tebl/ZX-Interface-2.021/gallery/2021-04-01 02.16.09.jpg

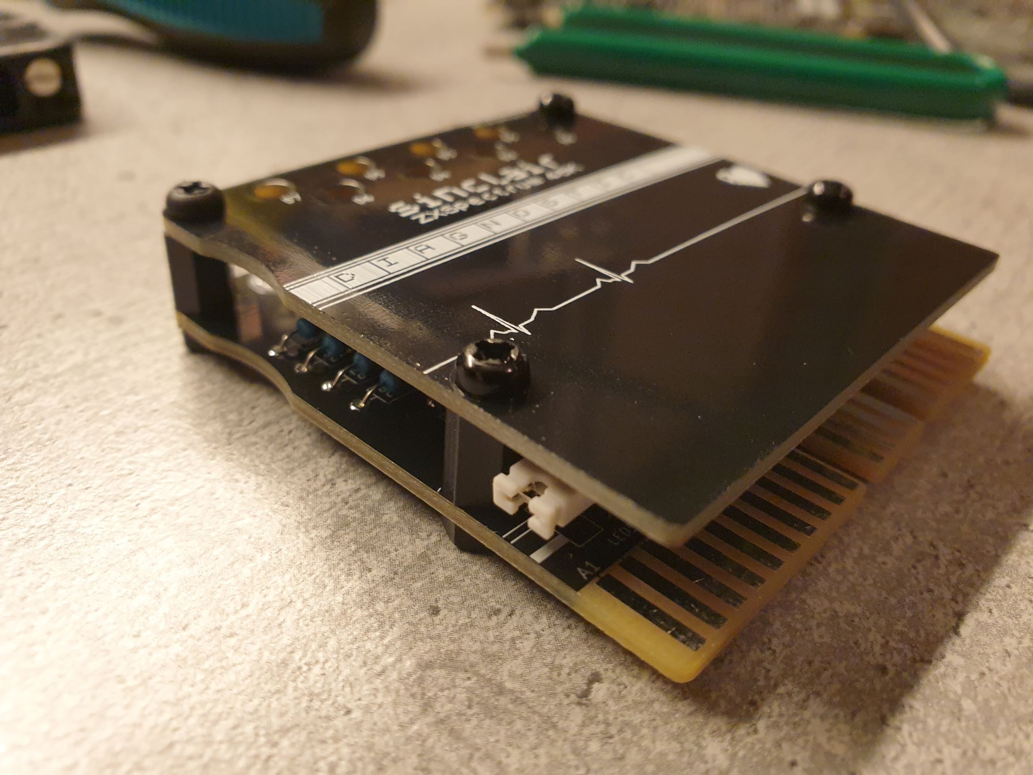
gallery/2021-04-01 02.16.09.jpg
