tebl/ZX-Interface-2.021/gallery/2021-04-01 15.58.48.jpg

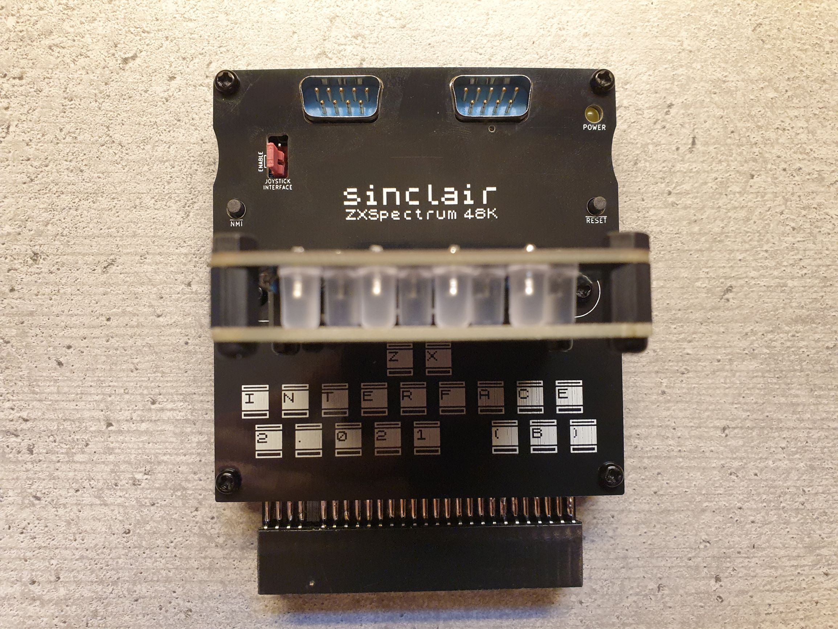
gallery/2021-04-01 15.58.48.jpg
