tebl/ZX-Interface-2.021/gallery/2021-04-01 22.12.05.jpg

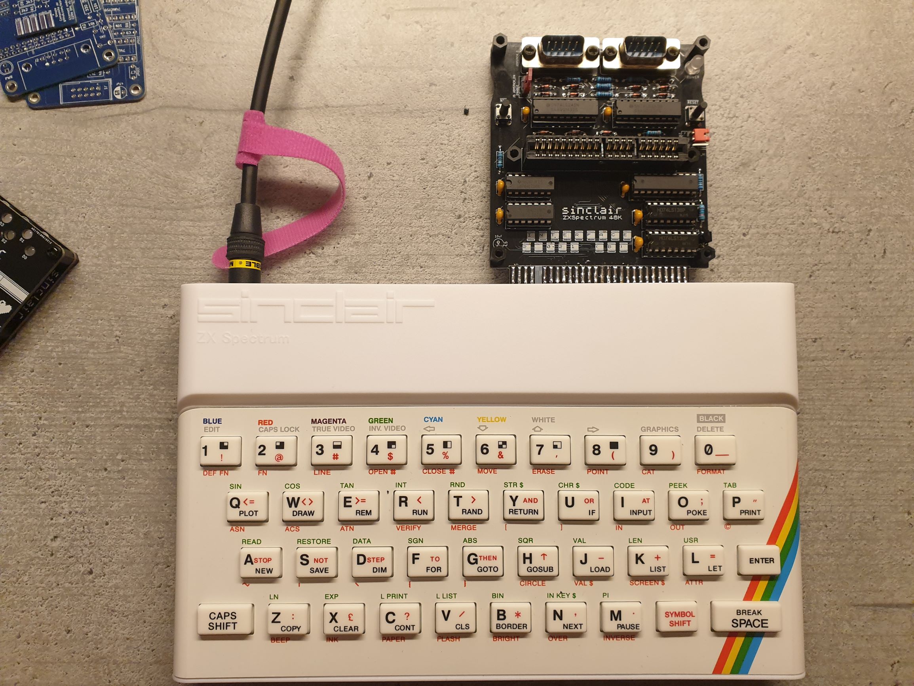
gallery/2021-04-01 22.12.05.jpg
