tebl/ZX-Interface-2.021/gallery/2021-04-01 22.18.30.jpg

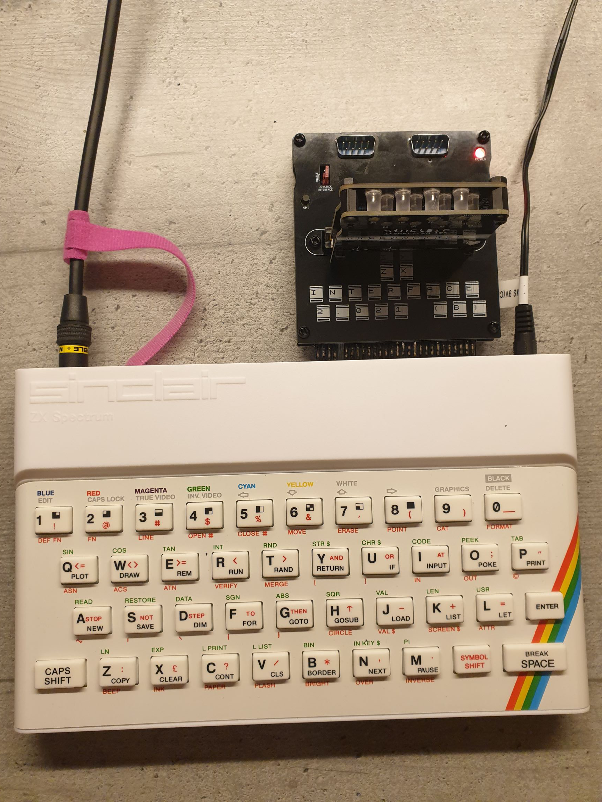
gallery/2021-04-01 22.18.30.jpg
