tebl/ZX-Interface-2.021/gallery/2021-04-14 02.23.00.jpg

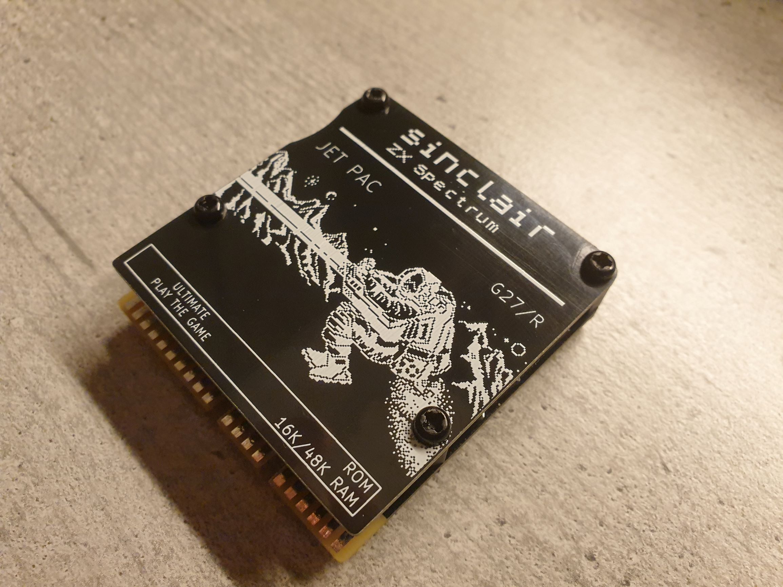
gallery/2021-04-14 02.23.00.jpg
