tebl/ZX-Interface-2.021/gallery/2021-04-23 00.03.16.jpg

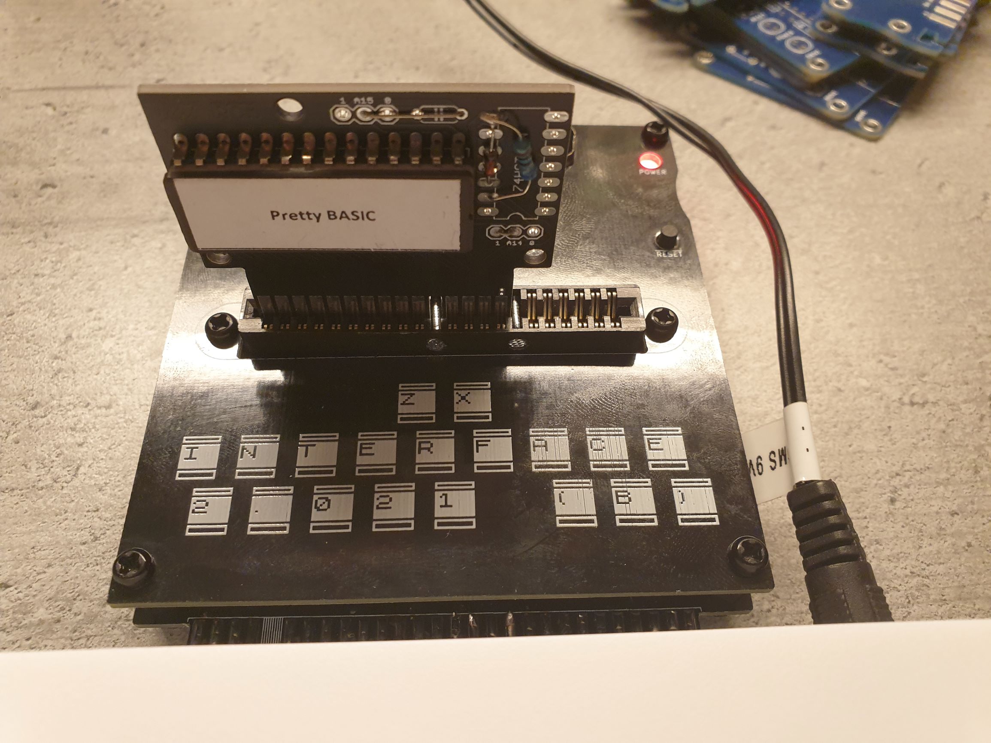
gallery/2021-04-23 00.03.16.jpg
