tebl/ZX-Interface-2.021/gallery/2021-04-29 00.07.34.jpg

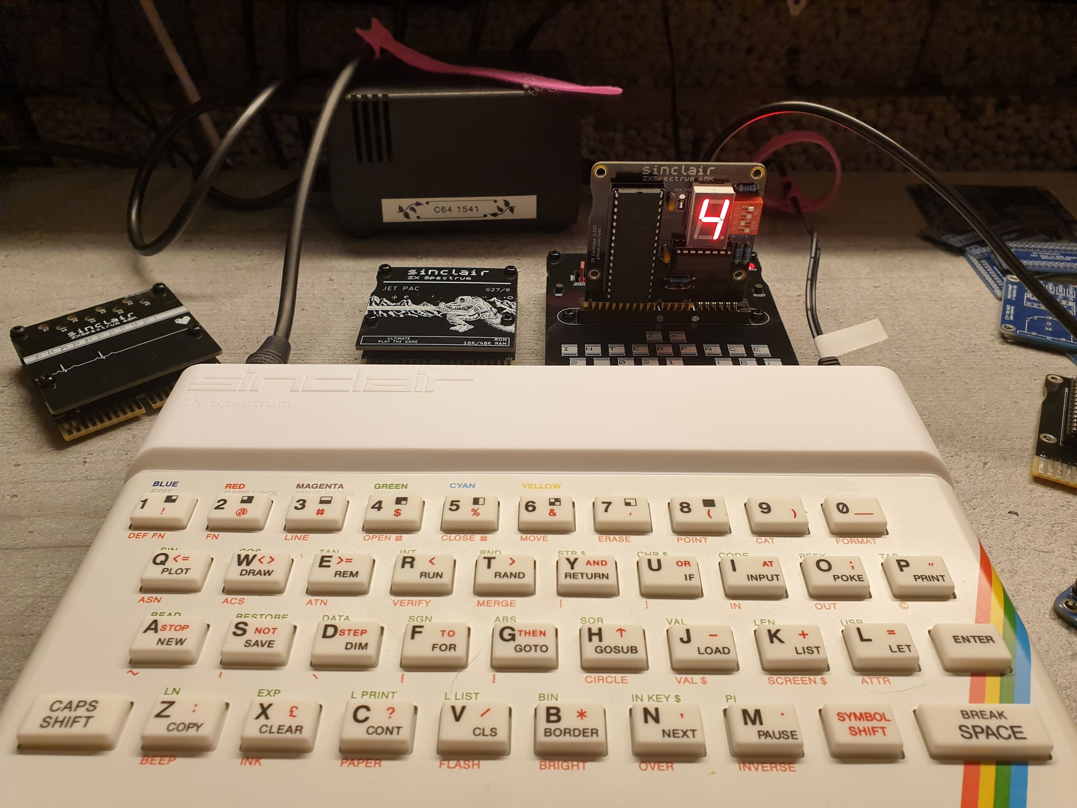
gallery/2021-04-29 00.07.34.jpg
