tebl/ZX-Interface-2.021/gallery/2021-05-09 21.05.03.jpg

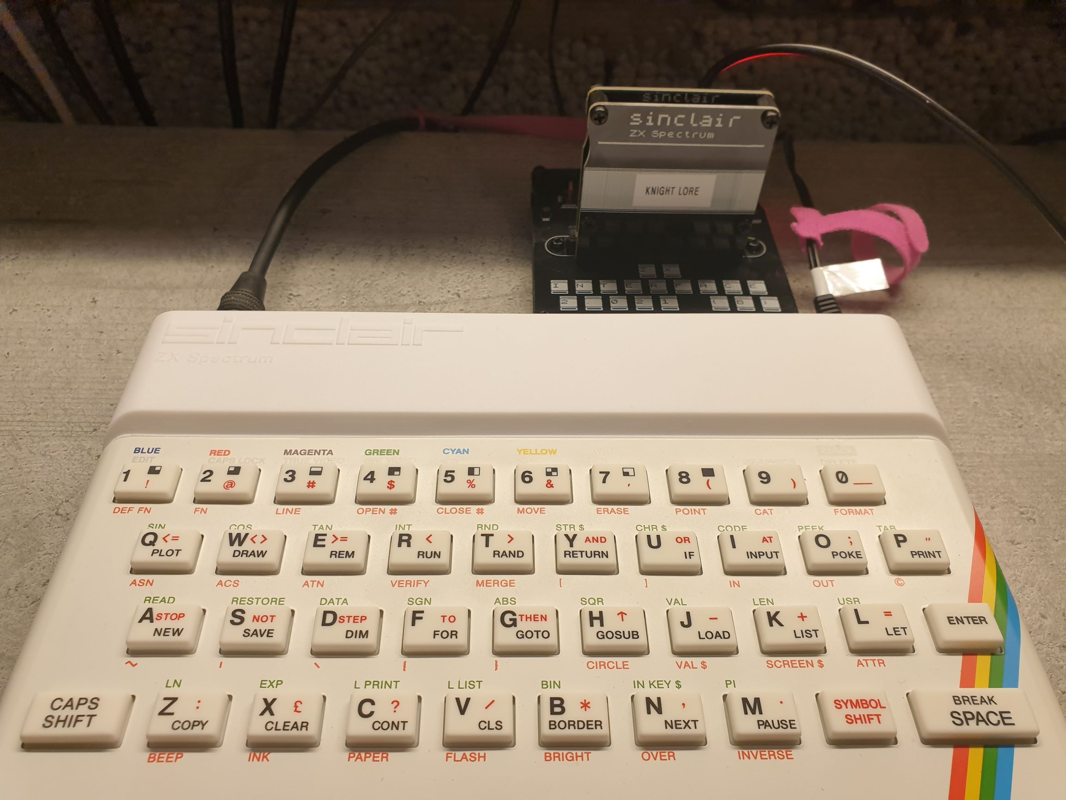
gallery/2021-05-09 21.05.03.jpg
