tebl/ZX-Interface-2.021/gallery/2021-09-04 23.34.56.jpg

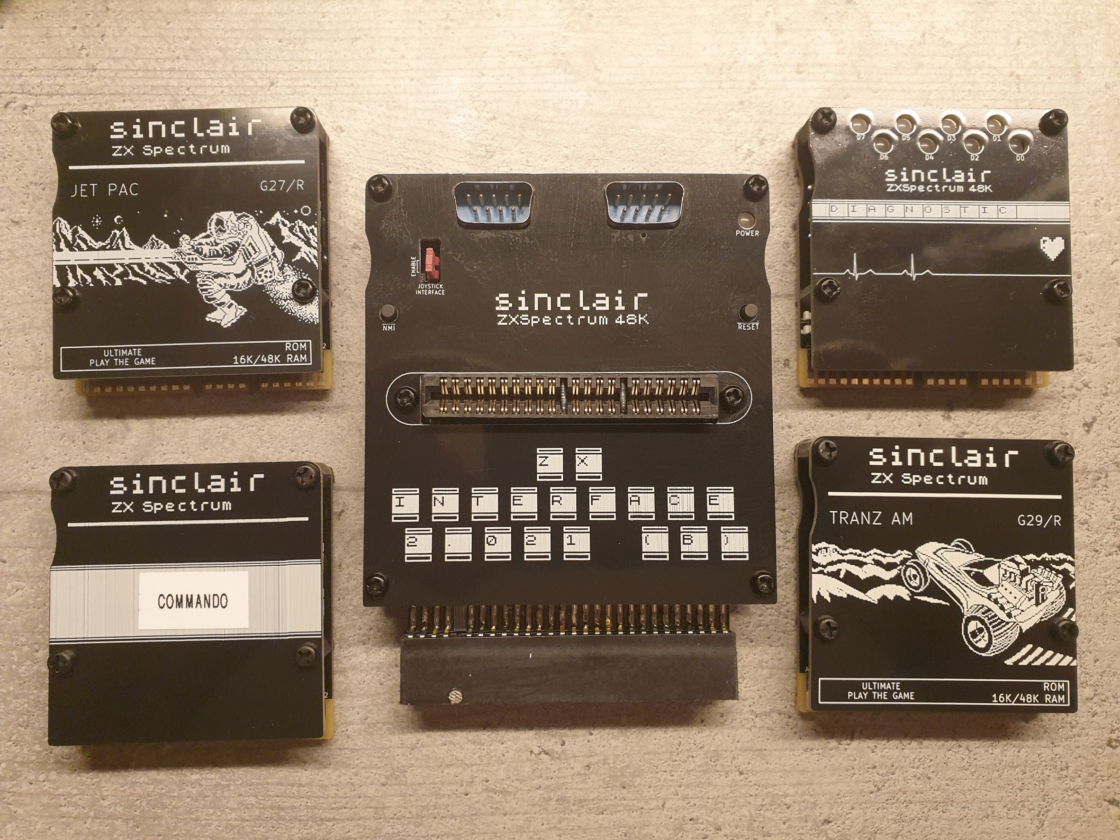
gallery/2021-09-04 23.34.56.jpg
