tebl/ZX-Interface-2.021/gallery/2021-09-04 23.39.01.jpg

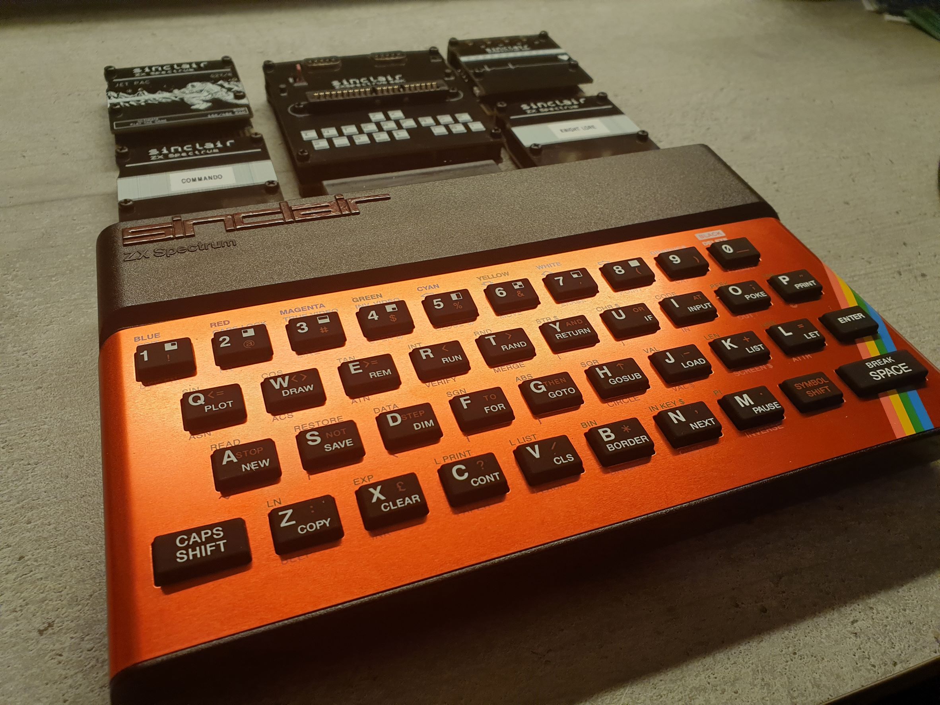
gallery/2021-09-04 23.39.01.jpg
