tebl/ZX-Interface-2.021/gallery/2021-09-06 23.09.44.jpg

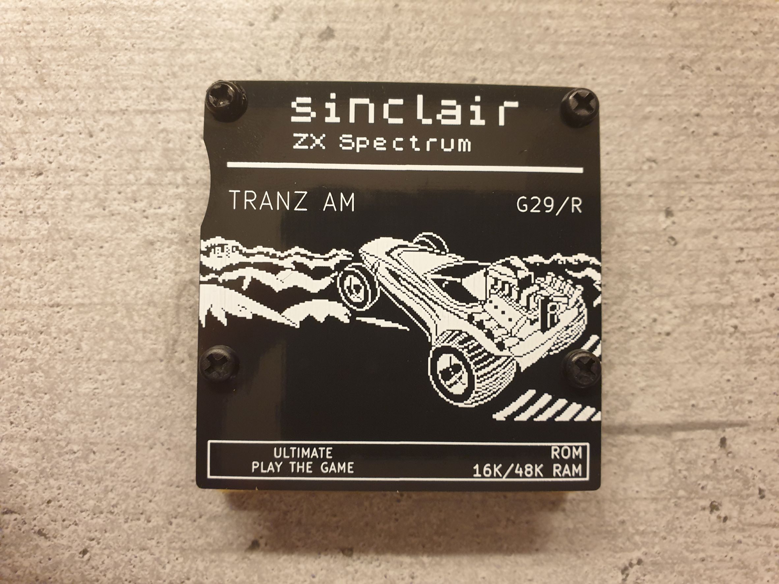
gallery/2021-09-06 23.09.44.jpg
