tebl/ZX-Interface-2.021/gallery/ZX Cartridge 2021 FA1.png

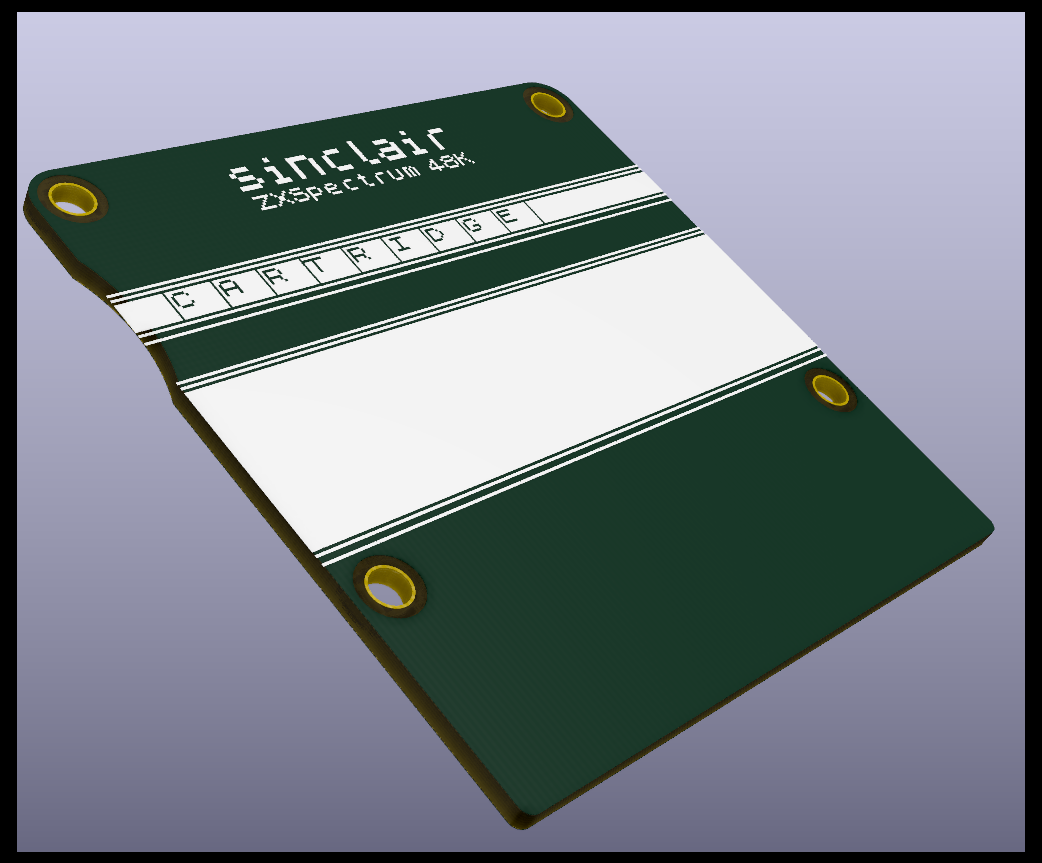
gallery/ZX Cartridge 2021 FA1.png
