tebl/ZX-Interface-2.021/gallery/ZX Cartridge 2021 FA1_001.jpg

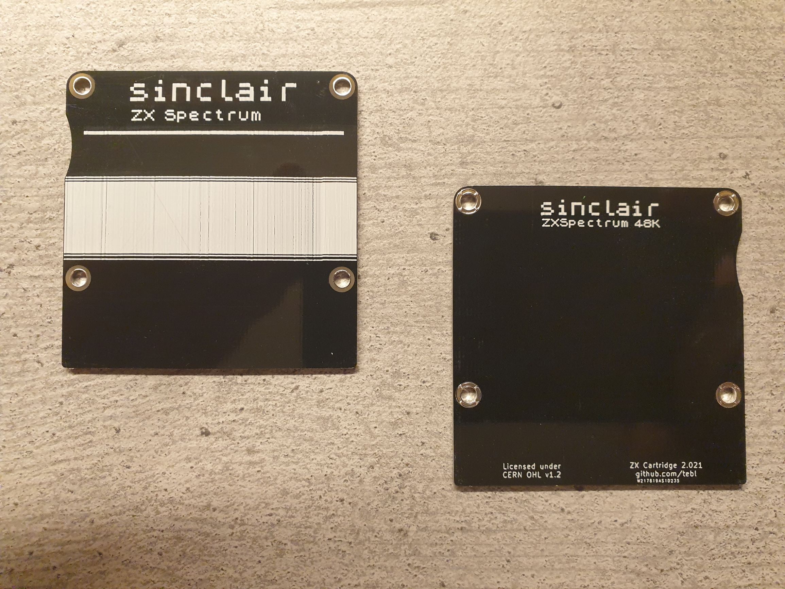
gallery/ZX Cartridge 2021 FA1_001.jpg
