tebl/ZX-Interface-2.021/gallery/ZX Cartridge 2021 FA1_003.jpg

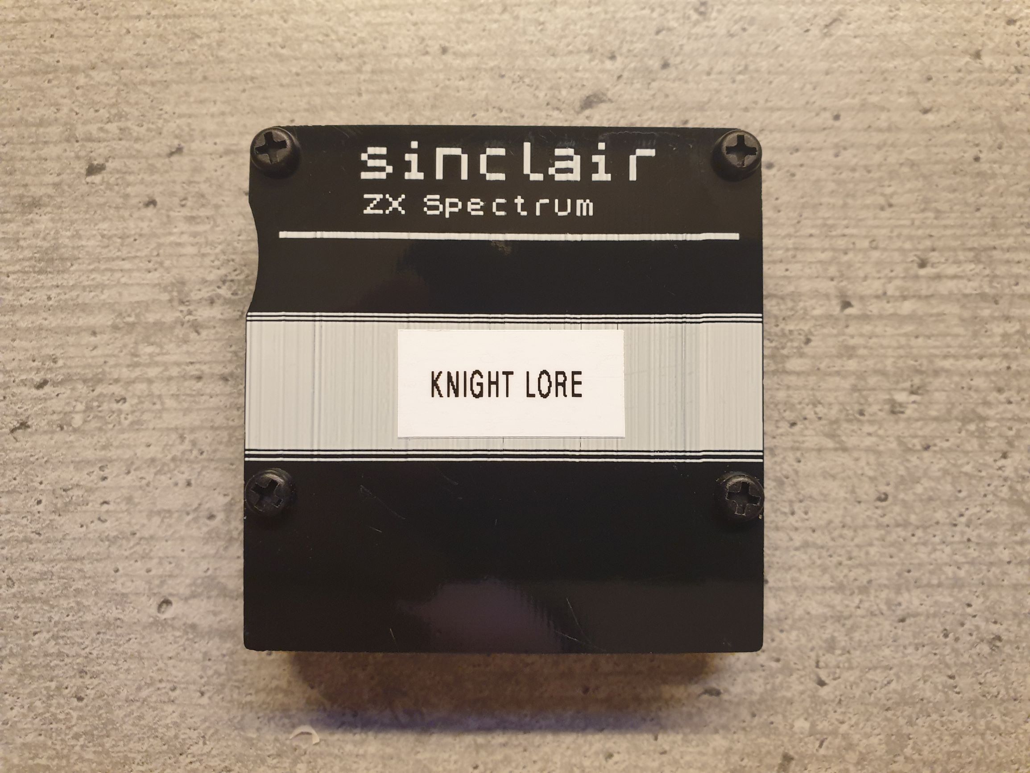
gallery/ZX Cartridge 2021 FA1_003.jpg
