tebl/ZX-Interface-2.021/gallery/ZX Cartridge 2021 FA5 Cassette.png

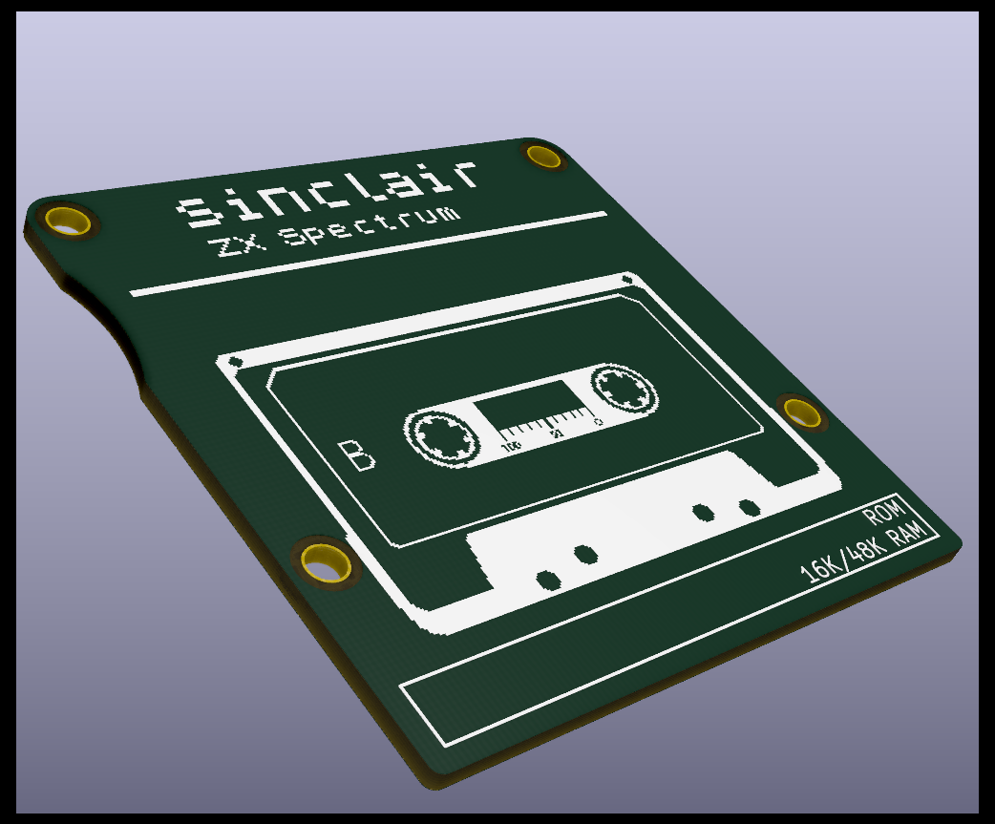
gallery/ZX Cartridge 2021 FA5 Cassette.png
