tebl/ZX-Interface-2.021/gallery/ZX Diagnostic 2021 FA1_001.jpg

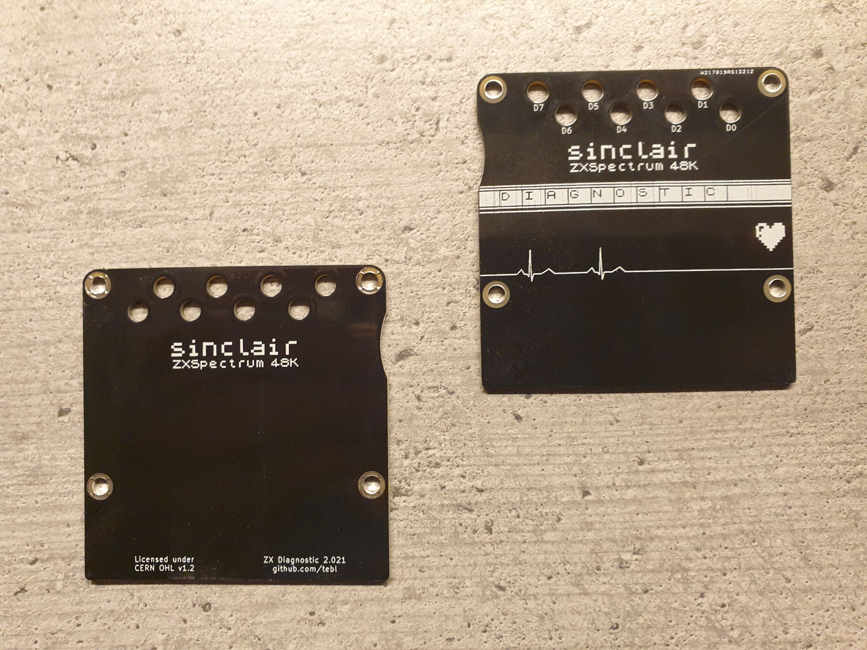
gallery/ZX Diagnostic 2021 FA1_001.jpg
