tebl/ZX-Interface-2.021/gallery/ZX Interface 2021 FA1.jpg

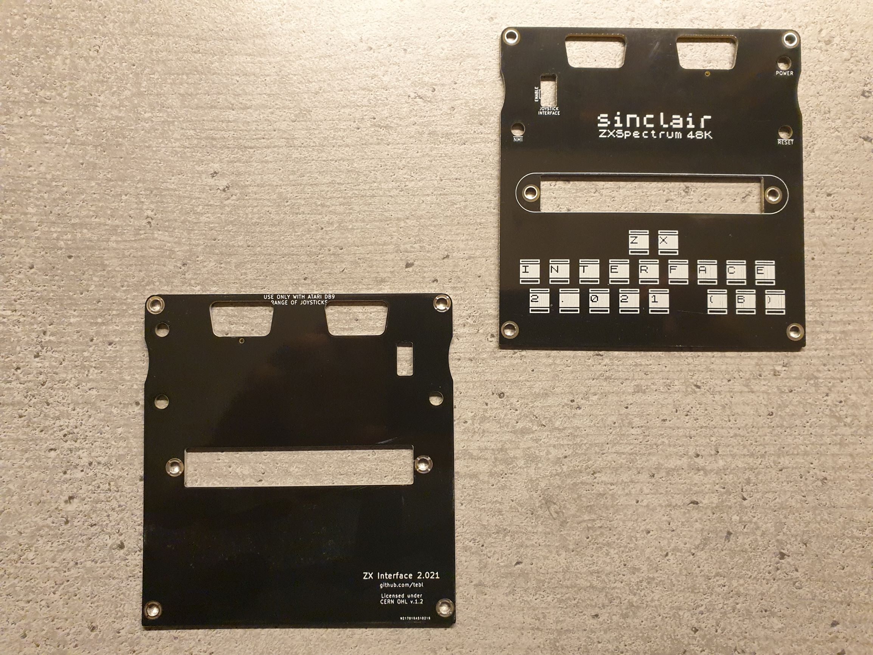
gallery/ZX Interface 2021 FA1.jpg
