tebl/ZX-Interface-2.021/gallery/ZX Interface 2021.png

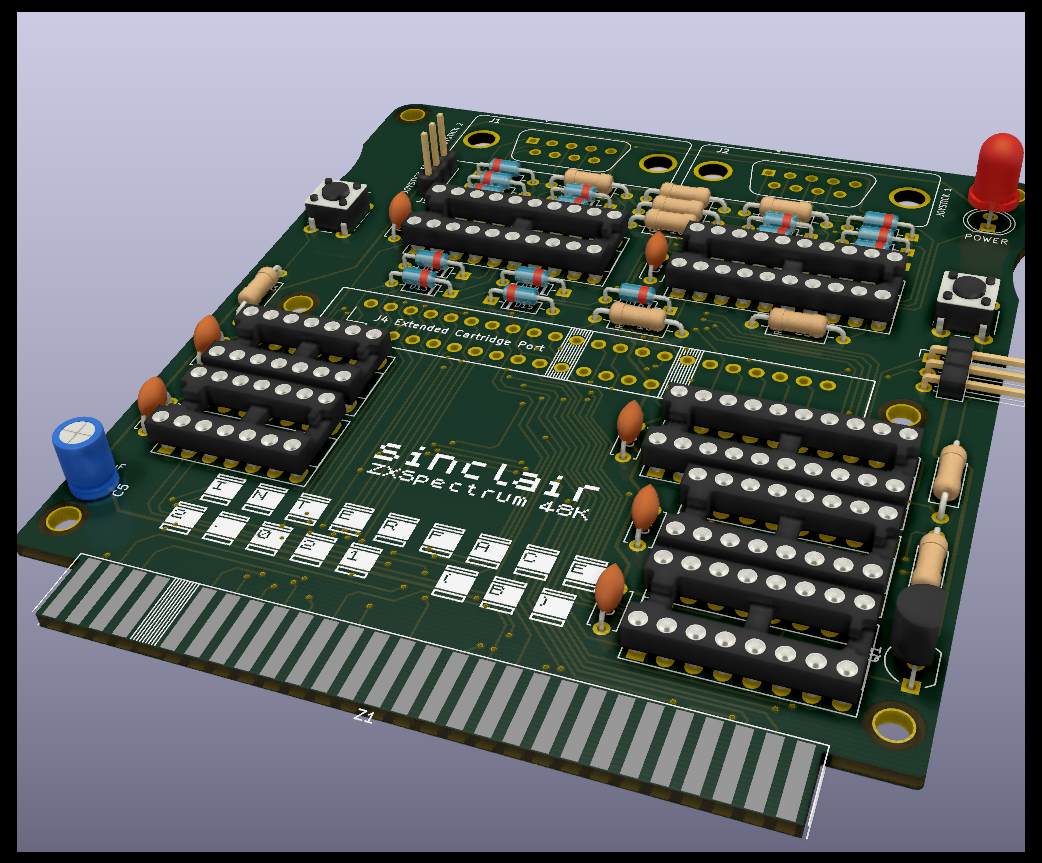
gallery/ZX Interface 2021.png
