tebl/ZX-Interface-2.021/software/snapshot_loader/snapshot_restored.png

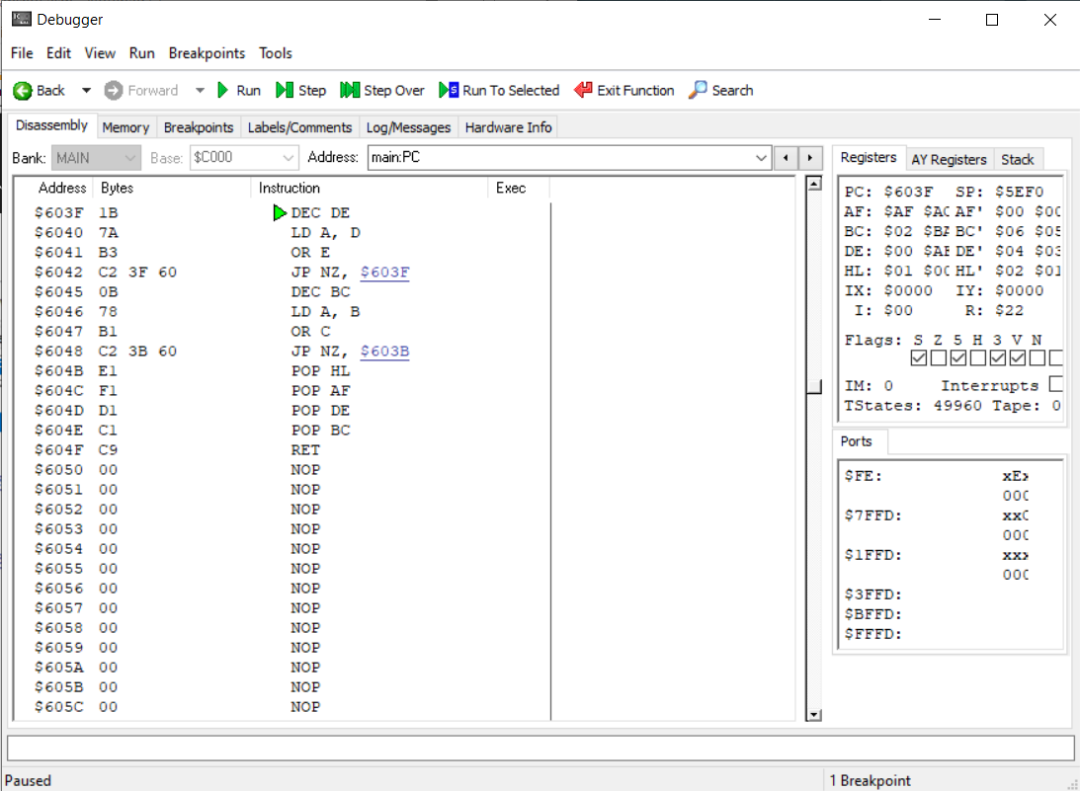
software/snapshot_loader/snapshot_restored.png
