tebl/ZX-Interface-2.021/software/snapshot_loader/snapshot_resume.png

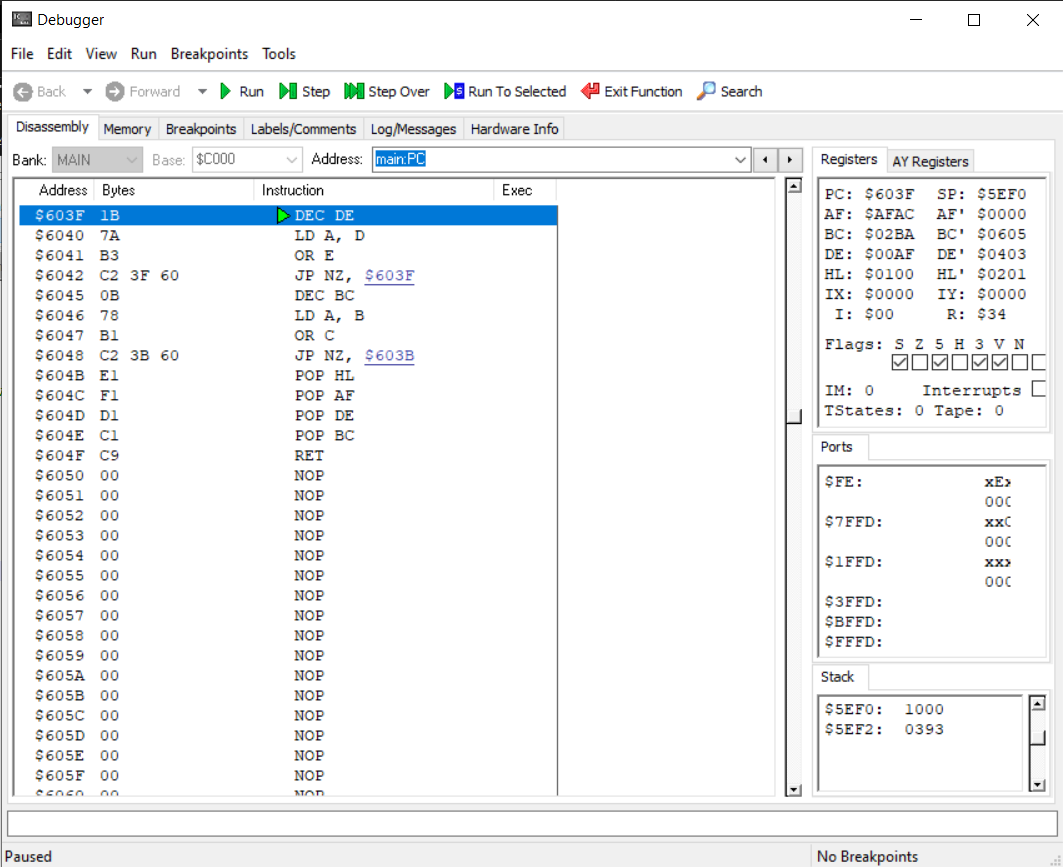
software/snapshot_loader/snapshot_resume.png
