tebl/ZX-Interface-2.021/gallery/build_cartridge_003.jpg

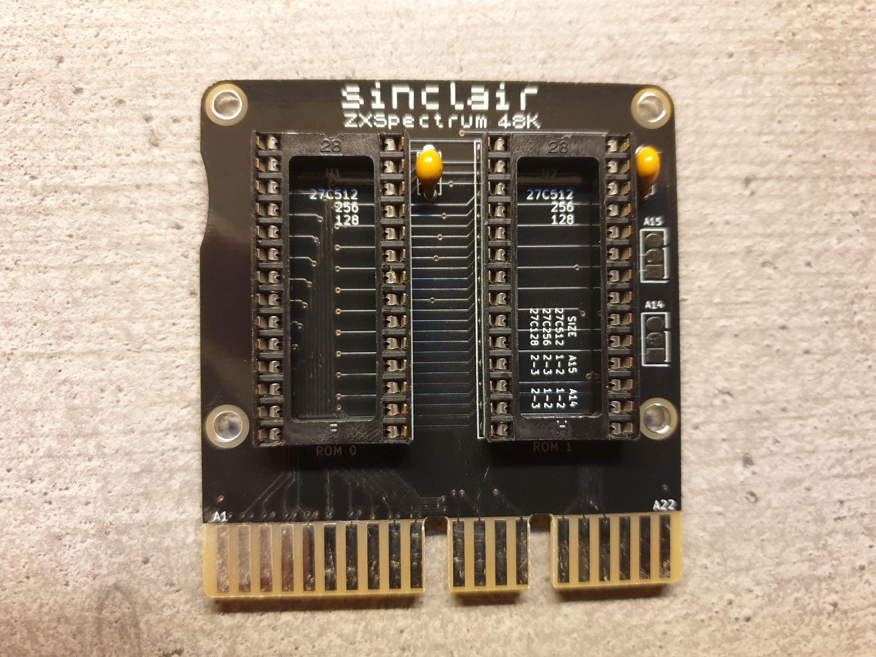
gallery/build_cartridge_003.jpg
