tebl/ZX-Interface-2.021/gallery/build_cartridge_1983_007.jpg

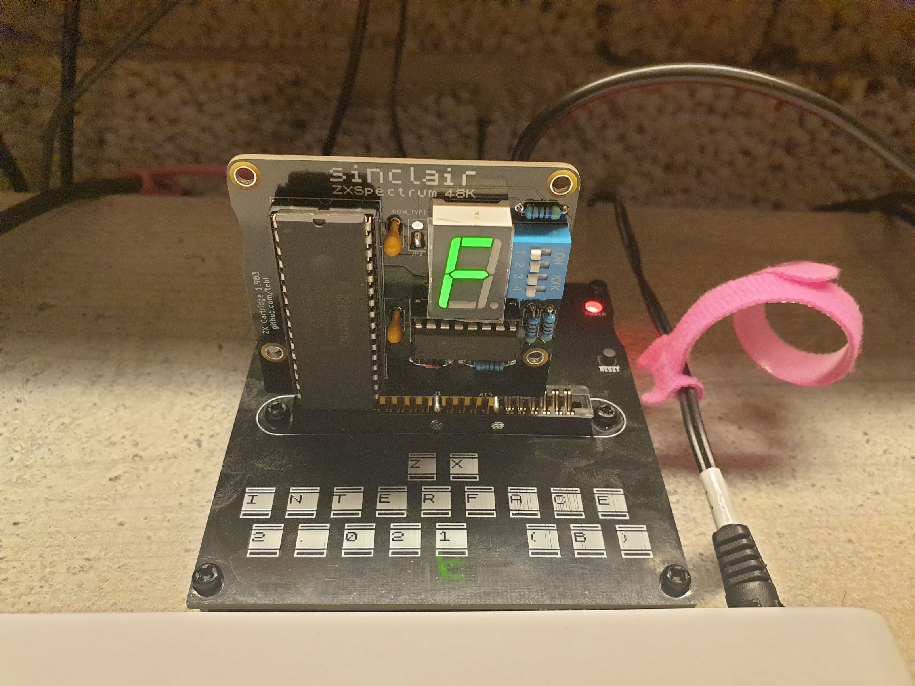
gallery/build_cartridge_1983_007.jpg
